edwindertien/picoLoraSEN66/src/config.cpp

#include "config.h"
#include <LittleFS.h>
#include <ArduinoJson.h>

Config cfg;

void loadConfig() {
    if (!LittleFS.exists("/config.json")) {
        Serial.println("[cfg] No config.json — using defaults");
        return;
    }
    File f = LittleFS.open("/config.json", "r");
    if (!f) return;

    JsonDocument doc;
    if (deserializeJson(doc, f) != DeserializationError::Ok) {
        Serial.println("[cfg] Parse error — using defaults");
        f.close(); return;
    }
    f.close();

    strlcpy(cfg.wifi_ssid, doc["wifi_ssid"] | "",              sizeof(cfg.wifi_ssid));
    strlcpy(cfg.wifi_pass, doc["wifi_pass"] | "",              sizeof(cfg.wifi_pass));
    strlcpy(cfg.ap_ssid,   doc["ap_ssid"]   | "SEN66-Monitor", sizeof(cfg.ap_ssid));
    strlcpy(cfg.ap_pass,   doc["ap_pass"]   | "sen66pass",     sizeof(cfg.ap_pass));
    cfg.interval_s = doc["interval_s"] | 10;
    cfg.log_max    = doc["log_max"]    | 1000;

    strlcpy(cfg.node_id, doc["node_id"] | "SEN66-01", sizeof(cfg.node_id));
    cfg.fan_cleaning     = doc["fan_cleaning"]    | true;
    cfg.wifi_force_ap    = doc["wifi_force_ap"]   | false;
    cfg.lora_freq        = doc["lora_freq"]       | 868.1f;
    cfg.lora_sf          = doc["lora_sf"]         | 9;
    cfg.lora_bw          = doc["lora_bw"]         | 125.0f;
    cfg.lora_power       = doc["lora_power"]      | 14;
    cfg.lora_interval_s  = doc["lora_interval_s"] | 60;
    cfg.lora_stream      = doc["lora_stream"]     | false;
    strlcpy(cfg.lora_dev_eui, doc["lora_dev_eui"] | "0000000000000000",                sizeof(cfg.lora_dev_eui));
    strlcpy(cfg.lora_app_eui, doc["lora_app_eui"] | "0000000000000000",                sizeof(cfg.lora_app_eui));
    strlcpy(cfg.lora_app_key, doc["lora_app_key"] | "00000000000000000000000000000000", sizeof(cfg.lora_app_key));
    strlcpy(cfg.lora_dev_eui, doc["lora_dev_eui"] | "0000000000000000",                sizeof(cfg.lora_dev_eui));
    strlcpy(cfg.lora_app_eui, doc["lora_app_eui"] | "0000000000000000",                sizeof(cfg.lora_app_eui));
    strlcpy(cfg.lora_app_key, doc["lora_app_key"] | "00000000000000000000000000000000", sizeof(cfg.lora_app_key));
    cfg.lora_interval_s = doc["lora_interval_s"] | 60;
    Serial.printf("[cfg] Loaded: ssid='%s' interval=%ds fan_clean=%s lora_freq=%.1f\n",
        cfg.wifi_ssid, cfg.interval_s,
        cfg.fan_cleaning ? "yes" : "no", cfg.lora_freq);
}

bool saveConfig() {
    File f = LittleFS.open("/config.json", "w");
    if (!f) return false;

    JsonDocument doc;
    doc["wifi_ssid"]  = cfg.wifi_ssid;
    doc["wifi_pass"]  = cfg.wifi_pass;
    doc["ap_ssid"]    = cfg.ap_ssid;
    doc["ap_pass"]    = cfg.ap_pass;
    doc["interval_s"]      = cfg.interval_s;
    doc["log_max"]         = cfg.log_max;
    doc["node_id"]         = cfg.node_id;
    doc["fan_cleaning"]    = cfg.fan_cleaning;
    doc["wifi_force_ap"]   = cfg.wifi_force_ap;
    doc["lora_freq"]       = cfg.lora_freq;
    doc["lora_sf"]         = cfg.lora_sf;
    doc["lora_bw"]         = cfg.lora_bw;
    doc["lora_power"]      = cfg.lora_power;
    doc["lora_interval_s"] = cfg.lora_interval_s;
    doc["lora_stream"]     = cfg.lora_stream;
    doc["lora_dev_eui"]    = cfg.lora_dev_eui;
    doc["lora_app_eui"]    = cfg.lora_app_eui;
    doc["lora_app_key"]    = cfg.lora_app_key;
    doc["lora_dev_eui"]    = cfg.lora_dev_eui;
    doc["lora_app_eui"]    = cfg.lora_app_eui;
    doc["lora_app_key"]    = cfg.lora_app_key;
    doc["lora_interval_s"] = cfg.lora_interval_s;
    serializeJson(doc, f);
    f.close();
    return true;
}
